joebmz98/MC8P-Midi-Controller/MC8P_MIDI_CONTROLLERS_MEDIA/DIAGRAMS/SSD1306_M2_Diagram_2.png

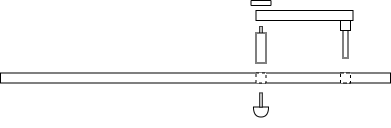
MC8P_MIDI_CONTROLLERS_MEDIA/DIAGRAMS/SSD1306_M2_Diagram_2.png
