joebmz98/MC8P-Midi-Controller/MC8P_MIDI_CONTROLLERS_MEDIA/DIAGRAMS/Stand-off_Mounting.png

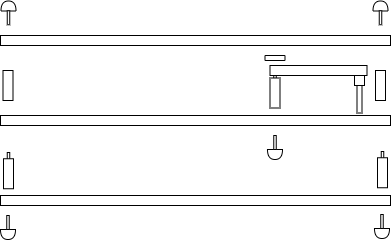
MC8P_MIDI_CONTROLLERS_MEDIA/DIAGRAMS/Stand-off_Mounting.png
