joebmz98/MC8P-Midi-Controller/MC8P_MIDI_CONTROLLERS_MEDIA/PHOTOS/20250831_105954.jpg

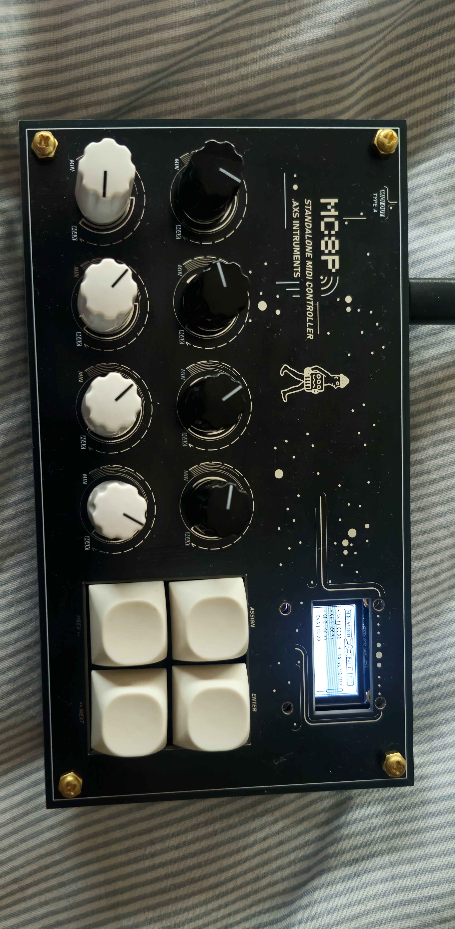
MC8P_MIDI_CONTROLLERS_MEDIA/PHOTOS/20250831_105954.jpg
