joebmz98/MC8P-Midi-Controller/MC8P_MIDI_CONTROLLERS_MEDIA/PHOTOS/P1155417.JPG

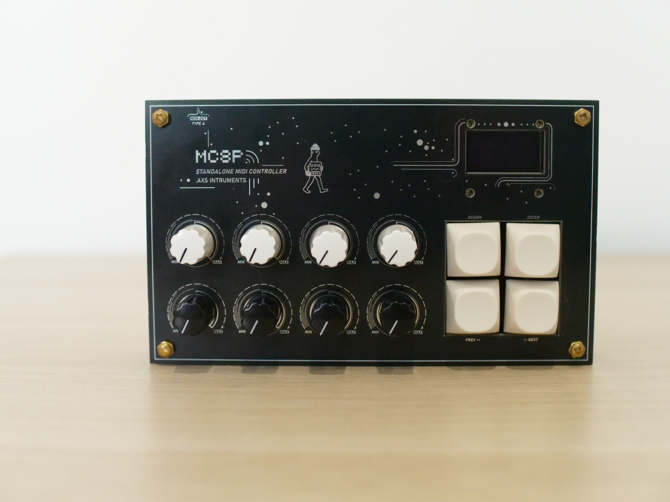
MC8P_MIDI_CONTROLLERS_MEDIA/PHOTOS/P1155417.JPG
