joebmz98/MC8P-Midi-Controller/MC8P_MIDI_CONTROLLERS_MEDIA/PHOTOS/P1155434.JPG

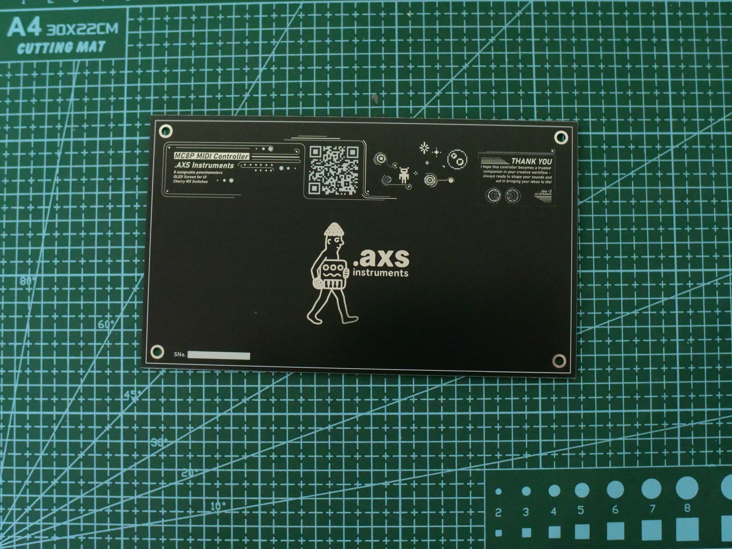
MC8P_MIDI_CONTROLLERS_MEDIA/PHOTOS/P1155434.JPG
